Pebblin/102b-Project/CAD/gearbox assembly.SLDASM

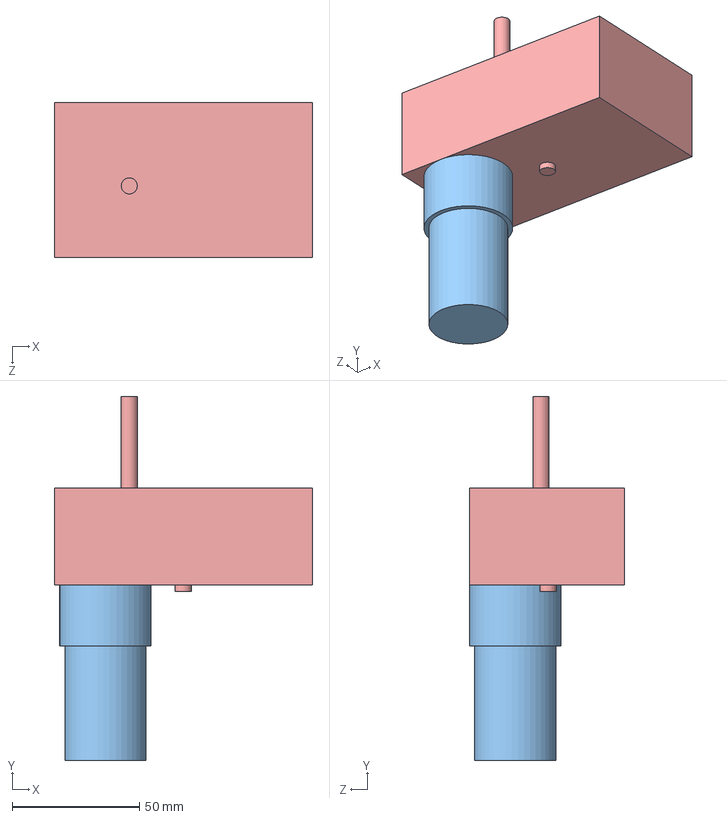
[picture p24: CAD file, 2024-11-25]
CAD/gearbox assembly.SLDASM
101.6 x 143.2 x 61.0 mm
housing
Inch - Spur gear 24DP 10T 20PA 0.5FW ---S10N3.0H2.0L0.25N x 2
motor
Inch - Spur gear 24DP 48T 20PA 0.5FW ---S48N3.0H2.0L0.03125N1
Inch - Spur gear 24DP 30T 20PA 0.25FW ---S30N3.0H2.0L0.25N
