Pebblin/102b-Project/CAD/housing.SLDPRT

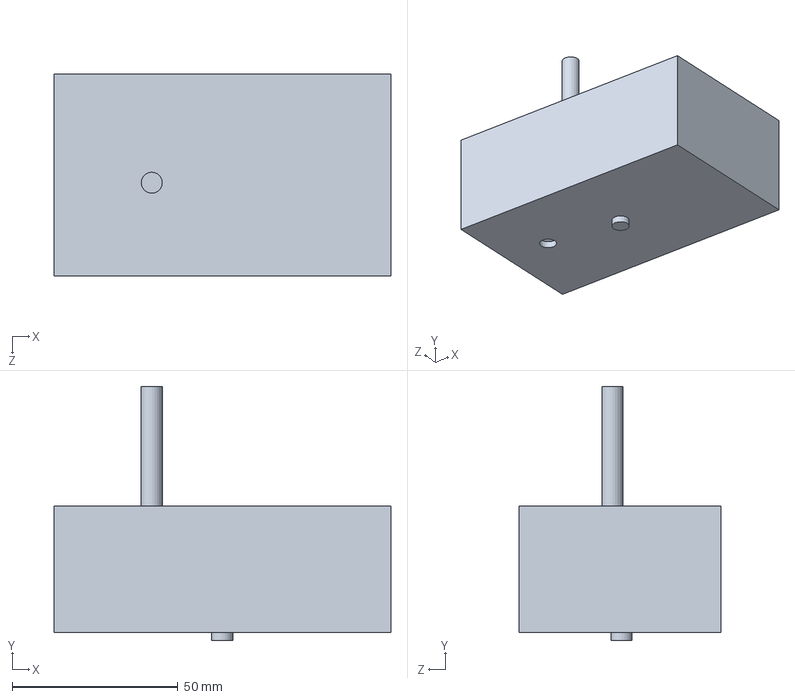
[picture p38: CAD file, 2024-11-25]
CAD/housing.SLDPRT
101.6 x 76.7 x 61.0 mm
