Pebblin/102b-Project/CAD/Inch - Spur gear 24DP 10T 20PA 0.5FW ---S10N3.0H2.0L0.25N.SLDPRT

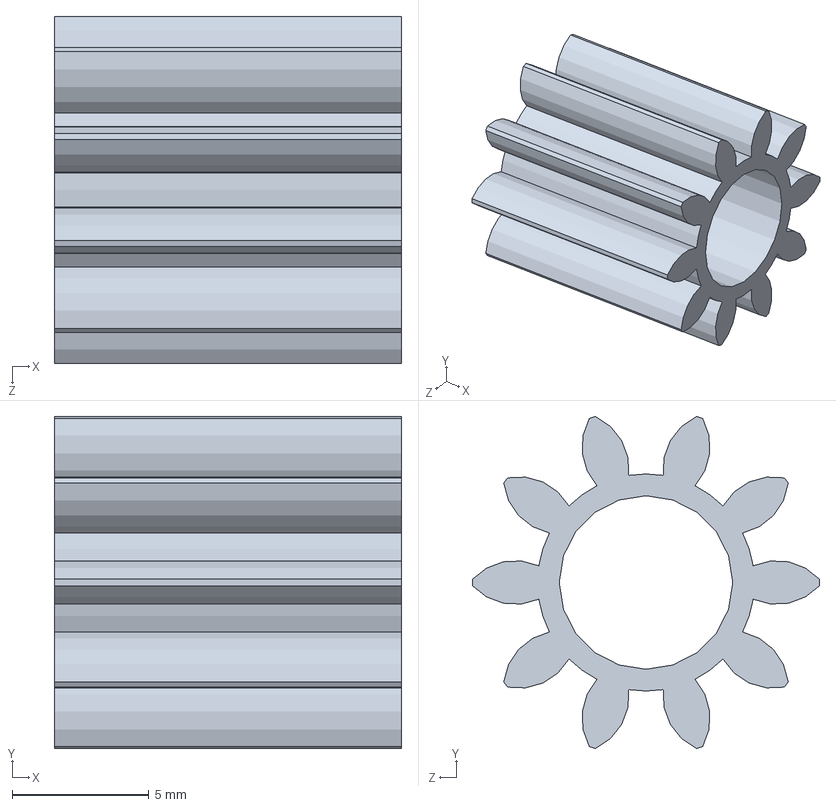
[picture p39: CAD file, 2024-11-25]
CAD/Inch - Spur gear 24DP 10T 20PA 0.5FW ---S10N3.0H2.0L0.25N.SLDPRT
12.7 x 12.2 x 12.7 mm
