Pebblin/102b-Project/CAD/ball 20mm.SLDPRT

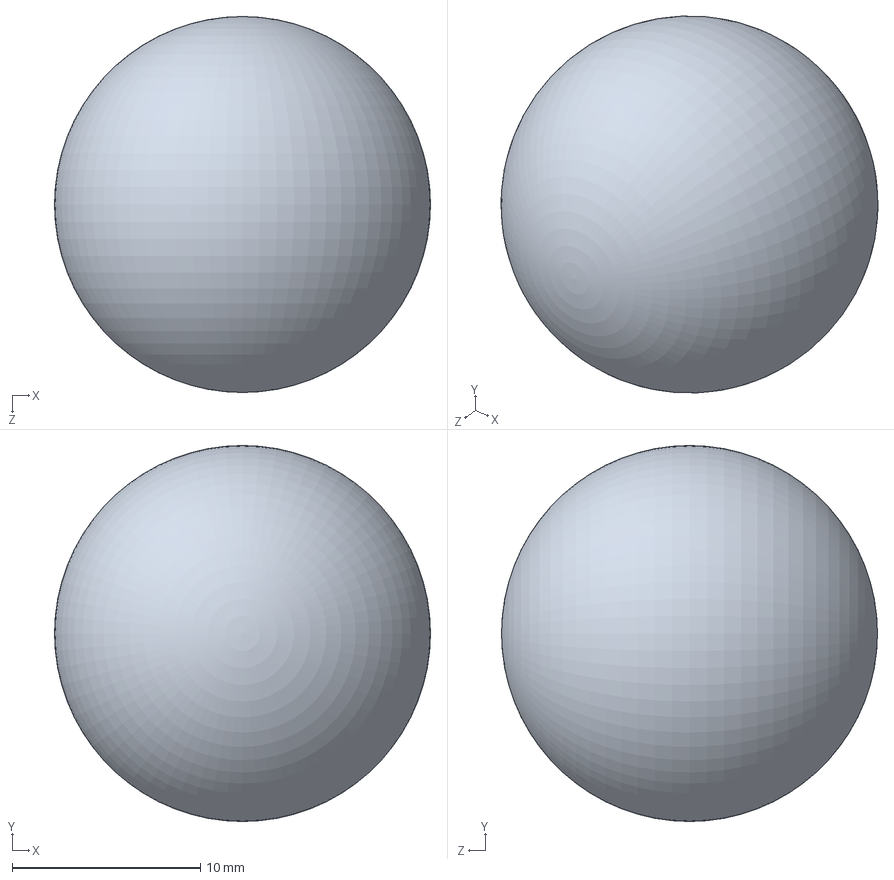
[picture p40: CAD file, 2024-11-25]
CAD/ball 20mm.SLDPRT
20.0 x 20.0 x 20.0 mm
